whosmatt/truecolors/components/storage/storage.c

// storage.c
#include "storage.h"

#include <string.h>
#include "appstate.h"
#include "app_config.h"
#include "app_events.h"
#include "nvs.h"
#include "esp_timer.h"
#include "esp_log.h"

static const char *TAG = "storage";

// v2: dropped power, the light always boots off.
#define SCENE_BLOB_VERSION 2

typedef struct {
    uint8_t  version;
    float    brightness;
    float    stretch;
    uint16_t effect_id;
    float    color[3];
    float    speed;
    float    audio_sens;
    float    params[EFFECT_PARAM_MAX];
} scene_blob_t;

static nvs_handle_t s_nvs;
static esp_timer_handle_t s_persist_timer;

static void persist_now(void *arg)
{
    app_state_t st;
    appstate_get(&st);

    scene_blob_t blob = {
        .version = SCENE_BLOB_VERSION,
        .brightness = st.brightness,
        .stretch = st.stretch,
        .effect_id = st.effect_id,
        .speed = st.speed,
        .audio_sens = st.audio_sens,
    };
    memcpy(blob.color, st.color, sizeof(blob.color));
    memcpy(blob.params, st.params, sizeof(blob.params));

    esp_err_t err = nvs_set_blob(s_nvs, NVS_KEY_SCENE, &blob, sizeof(blob));
    if (err == ESP_OK) {
        err = nvs_commit(s_nvs);
    }
    if (err != ESP_OK) {
        ESP_LOGW(TAG, "scene persist failed: %s", esp_err_to_name(err));
    }
}

static void on_state_changed(void *arg, esp_event_base_t base, int32_t id, void *data)
{
    const app_state_changed_evt_t *evt = data;
    if (evt && evt->src == APP_SRC_STORAGE_RESTORE) {
        return;
    }
    // Power is not persisted, so a pure on/off toggle skips the flash write.
    if (evt && (evt->changed_mask & ~STATE_F_POWER) == 0) {
        return;
    }
    esp_timer_stop(s_persist_timer);
    esp_timer_start_once(s_persist_timer, (uint64_t)PERSIST_DEBOUNCE_MS * 1000);
}

esp_err_t storage_init(void)
{
    esp_err_t err = nvs_open(NVS_NAMESPACE, NVS_READWRITE, &s_nvs);
    if (err != ESP_OK) {
        ESP_LOGE(TAG, "nvs_open failed: %s", esp_err_to_name(err));
        return err;
    }

    const esp_timer_create_args_t targs = {
        .callback = persist_now,
        .name = "scene_persist",
    };
    return esp_timer_create(&targs, &s_persist_timer);
}

esp_err_t storage_restore_scene(void)
{
    esp_err_t err = app_bus_subscribe(EVT_STATE_CHANGED, on_state_changed, NULL);
    if (err != ESP_OK) {
        ESP_LOGW(TAG, "subscribe failed: %s", esp_err_to_name(err));
    }

    scene_blob_t blob;
    size_t len = sizeof(blob);
    err = nvs_get_blob(s_nvs, NVS_KEY_SCENE, &blob, &len);
    if (err != ESP_OK || len != sizeof(blob) || blob.version != SCENE_BLOB_VERSION) {
        ESP_LOGI(TAG, "no saved scene, using defaults");
        return ESP_OK;
    }

    app_patch_t patch = {
        .mask = STATE_F_BRIGHTNESS | STATE_F_STRETCH |
                STATE_F_EFFECT | STATE_F_COLOR | STATE_F_SPEED |
                STATE_F_AUDIO_SENS | STATE_F_PARAMS,
        .brightness = blob.brightness,
        .stretch = blob.stretch,
        .effect_id = blob.effect_id,
        .speed = blob.speed,
        .audio_sens = blob.audio_sens,
    };
    memcpy(patch.color, blob.color, sizeof(patch.color));
    memcpy(patch.params, blob.params, sizeof(patch.params));

    return appstate_apply_patch(APP_SRC_STORAGE_RESTORE, &patch);
}

esp_err_t storage_save_pwm_hz(uint32_t hz)
{
    esp_err_t err = nvs_set_u32(s_nvs, NVS_KEY_PWM_HZ, hz);
    return err == ESP_OK ? nvs_commit(s_nvs) : err;
}

uint32_t storage_load_pwm_hz(void)
{
    uint32_t hz = TC_PWM_HZ;
    nvs_get_u32(s_nvs, NVS_KEY_PWM_HZ, &hz);
    return hz;
}

esp_err_t storage_save_epilepsy_safe(bool on)
{
    esp_err_t err = nvs_set_u8(s_nvs, NVS_KEY_EPI_SAFE, on ? 1 : 0);
    return err == ESP_OK ? nvs_commit(s_nvs) : err;
}

bool storage_load_epilepsy_safe(void)
{
    uint8_t on = 1;
    nvs_get_u8(s_nvs, NVS_KEY_EPI_SAFE, &on);
    return on != 0;
}

esp_err_t storage_save_wifi(const char *ssid, const char *pass)
{
    esp_err_t err = nvs_set_str(s_nvs, NVS_KEY_WIFI_SSID, ssid ? ssid : "");
    if (err == ESP_OK) {
        err = nvs_set_str(s_nvs, NVS_KEY_WIFI_PASS, pass ? pass : "");
    }
    if (err == ESP_OK) {
        err = nvs_commit(s_nvs);
    }
    return err;
}

bool storage_load_wifi(char *ssid, size_t ssid_len, char *pass, size_t pass_len)
{
    if (nvs_get_str(s_nvs, NVS_KEY_WIFI_SSID, ssid, &ssid_len) != ESP_OK) {
        return false;
    }
    if (nvs_get_str(s_nvs, NVS_KEY_WIFI_PASS, pass, &pass_len) != ESP_OK) {
        pass[0] = '\0';
    }
    return ssid[0] != '\0';
}

void storage_clear_all(void)
{
    nvs_erase_all(s_nvs);
    nvs_commit(s_nvs);
}
