whosmatt/truecolors/components/sysmgr/sysmgr_safety.c

// sysmgr_safety.c
#include "sysmgr_safety.h"
#include "app_config.h"

void safety_init(safety_state_t *st)
{
    st->overtemp_latched = false;
    st->fanstall_latched = false;
    st->stall_timer_s = 0.0f;
    st->boot_gate_cleared = false;
}

void safety_step(safety_state_t *st, const safety_inputs_t *in,
                 float dt, safety_output_t *out)
{
    uint32_t warn = 0;
    uint32_t err = 0;

    // A bad NTC reading is treated as overtemp: thermal protection is gone.
    bool overtemp = (!in->ntc_valid) || (in->ntc_temp_c >= T_LIMIT_C);
    if (overtemp) {
        st->overtemp_latched = true;
    }

    // Fan stall: the fan must always spin (fancontrol bursts FAN_KICK_DUTY
    // whenever the tach is silent). Silence is a warning while the spin-up
    // attempt runs; it latches as an error once the attempt has failed.
    if (in->fan_rpm == 0) {
        st->stall_timer_s += dt;
        if (st->stall_timer_s >= STALL_FAIL_S) {
            st->fanstall_latched = true;
        }
        if (st->stall_timer_s >= STALL_WARN_S) {
            warn |= SF_FAN_STALL;
        }
    } else {
        st->stall_timer_s = 0.0f;
    }

    if (st->overtemp_latched) {
        err |= SF_OVERTEMP;
    }
    if (st->fanstall_latched) {
        err |= SF_FAN_STALL;
    }
    bool latched = st->overtemp_latched || st->fanstall_latched;

    bool conditions_ok = in->ntc_valid && in->ntc_temp_c < T_LIMIT_C;
    if (conditions_ok) {
        st->boot_gate_cleared = true;
    }

    if (!in->pd_ok) {
        warn |= SF_PD_LOST;
    }

    float scale;
    if (latched || !st->boot_gate_cleared) {
        scale = 0.0f;
    } else {
        scale = 1.0f;
    }

    // Warning only, we rely on the PD source to restart in an overcurrent condition, sending the light back to its default OFF state. 
    float required_a = LASER_A_INTERCEPT + LASER_A_PER_VOLT * in->vin_v + LASER_A_MARGIN;
    if (in->pd_ok && in->pd_current_a < required_a) {
        warn |= SF_UNDERCURRENT;
    }

    if (in->vin_v < VIN_WARN_V) {
        warn |= SF_VIN_LOW;
    }

    out->safety_scale = scale;
    out->warn_flags = warn;
    out->err_flags = err;
    out->latched = latched;
}
