whosmatt/truecolors/components/laser/include/laser.h

// laser.h
// MCPWM RGB laser driver
// Staggered PWM with optional stretching to 100% combined duty

#pragma once

#include <stdbool.h>
#include "esp_err.h"

#ifdef __cplusplus
extern "C" {
#endif

// Configure MCPWM (timer, 3 operators), all widths 0, generators forced LOW.
esp_err_t laser_init(void);

// Set the three channels (linear 0..1) and the temporal stretch (0..1).
// Computes staggered widths and loads them atomically on the next TEZ.
// keepalive floors dark channels at MIN_ON pulses so the LM3409 bias stays
// awake: an EN held low decays VCC into low-power shutdown, and the recovery
// shows as a fade on the next turn-on.
void laser_set(float r, float g, float b, float stretch, bool keepalive);

// Force all generators LOW immediately (bypasses TEZ) on a FAULT transition.
void laser_emergency_off(void);

// Change the PWM frequency at runtime, glitch-free (period and comparators
// swap on the same TEZ). Valid range 80..2000 Hz.
esp_err_t laser_set_pwm_hz(uint32_t hz);
uint32_t laser_get_pwm_hz(void);

#ifdef __cplusplus
}
#endif
